Tinkerforge/piezo-speaker-v2-bricklet/software/src/configs/config_custom_bootloader.h

/* piezo-speaker-v2-bricklet
 * Copyright (C) 2018 Olaf Lüke <olaf@tinkerforge.com>
 *
 * config_custom_bootloader.h: Bootloader configurations for
 *                             Piezo Speaker Bricklet 2.0
 *
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
 * You should have received a copy of the GNU Lesser General Public
 * License along with this library; if not, write to the
 * Free Software Foundation, Inc., 59 Temple Place - Suite 330,
 * Boston, MA 02111-1307, USA.
 */

#ifndef CONFIG_CUSTOM_BOOTLOADER_H
#define CONFIG_CUSTOM_BOOTLOADER_H

#include "xmc_gpio.h"

// --- Basic defines ---
#define BOOTLOADER_DEVICE_IDENTIFIER   2145
#define BOOTLOADER_HW_VERSION_MAJOR    1
#define BOOTLOADER_HW_VERSION_MINOR    0
#define BOOTLOADER_HW_VERSION_REVISION 0

#define BOOTLOADER_STATUS_LED_PIN      P2_10
#define BOOTLOADER_BOOT_PAD_PIN        P2_9

#define BOOTLOADER_FLASH_EEPROM_SIZE   (4*256)
#define BOOTLOADER_FLASH_SIZE          (16*1024 - BOOTLOADER_FLASH_EEPROM_SIZE)

#define BOOTLOADER_FIX_POINTER_END


// --- SPITFP ---
#define SPITFP_USIC_CHANNEL         USIC0_CH1
#define SPITFP_USIC                 XMC_SPI0_CH1

#define SPITFP_SCLK_PIN             P1_3
#define SPITFP_SCLK_INPUT           XMC_USIC_CH_INPUT_DX1
#define SPITFP_SCLK_SOURCE          0b000 // DX1A

#define SPITFP_SELECT_PIN           P0_9
#define SPITFP_SELECT_INPUT         XMC_USIC_CH_INPUT_DX2
#define SPITFP_SELECT_SOURCE        0b001 // DX2B

#define SPITFP_MOSI_PIN             P1_2
#define SPITFP_MOSI_INPUT           XMC_USIC_CH_INPUT_DX0
#define SPITFP_MOSI_SOURCE          0b001 // DX0B

#define SPITFP_MISO_PIN             P0_7
#define SPITFP_MISO_PIN_AF          (XMC_GPIO_MODE_OUTPUT_PUSH_PULL_ALT7 | P0_7_AF_U0C1_DOUT0)

#define SPITFP_RECEIVE_BUFFER_SIZE  1024
#define SPITFP_RECEIVE_BUFFER_MASK  (SPITFP_RECEIVE_BUFFER_SIZE-1) // If size is power of 2

#define SPITFP_SERVICE_REQUEST_RX   0
#define SPITFP_SERVICE_REQUEST_TX   1

#define SPITFP_IRQ_RX               9
#define SPITFP_IRQ_RX_PRIORITY      2
#define SPITFP_IRQ_TX               10
#define SPITFP_IRQ_TX_PRIORITY      3

#define SPITFP_TX_DATA_POINTER      16
#define SPITFP_TX_SIZE              XMC_USIC_CH_FIFO_SIZE_16WORDS
#define SPITFP_TX_LIMIT             8

#define SPITFP_RX_DATA_POINTER      0
#define SPITFP_RX_SIZE              XMC_USIC_CH_FIFO_SIZE_16WORDS
#define SPITFP_RX_LIMIT             0

// --- BOOTLOADER FUNCTIONS ---

// define bootloader functions to put them into the BootloaderFunctions struct
// These functions are in the bootloader code and can be used from the firmware

#define BOOTLOADER_FUNCTION_SPITFP_TICK
#define BOOTLOADER_FUNCTION_SEND_ACK_AND_MESSAGE
#define BOOTLOADER_FUNCTION_SPITFP_IS_SEND_POSSIBLE
#define BOOTLOADER_FUNCTION_AEABI_IDIV
#define BOOTLOADER_FUNCTION_AEABI_UIDIV
#define BOOTLOADER_FUNCTION_AEABI_IDIVMOD
#define BOOTLOADER_FUNCTION_AEABI_UIDIVMOD
#define BOOTLOADER_FUNCTION_GET_UID
#define BOOTLOADER_FUNCTION_READ_EEPROM_PAGE
#define BOOTLOADER_FUNCTION_WRITE_EEPROM_PAGE

#endif
